Dilan-Wijesinghe/BMoTheModularRobot/CAD/MMo/Mmo_top.step

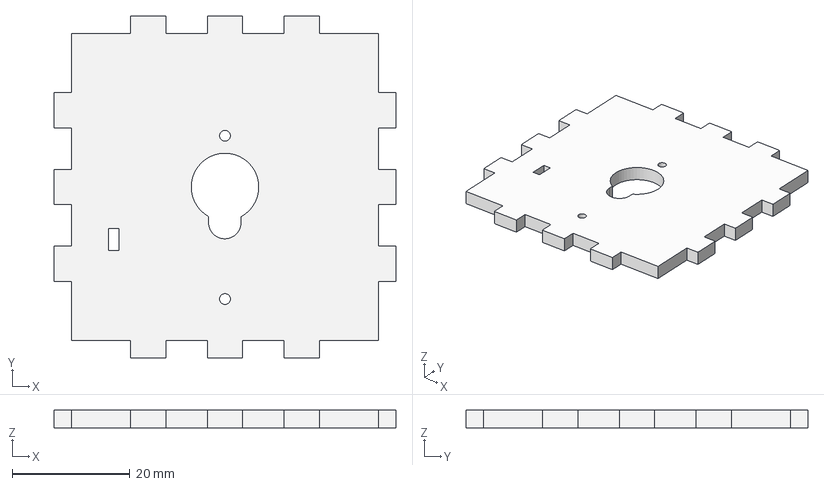
[picture p15: CAD file, 2023-03-17]
CAD/MMo/Mmo_top.step
58.0 x 58.0 x 3.00 mm
