Dilan-Wijesinghe/BMoTheModularRobot/CAD/HMo/Hmo_Top_Wall.step

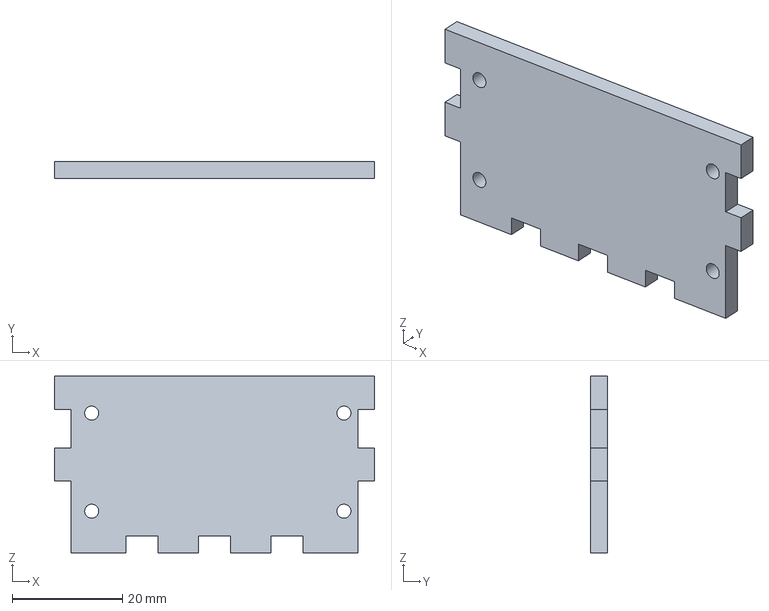
[picture p16: CAD file, 2023-03-17]
CAD/HMo/Hmo_Top_Wall.step
58.0 x 3.00 x 32.0 mm
